luk6xff/GarageDoorKeypad/keypad/Src/StateMachine/state_processing.h

/*
 * state_processing.h
 *
 *  Created on: Jul 22, 2021
 *      Author: luk6xff
 */

#ifndef STATEMACHINE_STATE_PROCESSING_H_
#define STATEMACHINE_STATE_PROCESSING_H_

#include "sm.h"

void state_processing(SmCtx *sm);


#endif /* STATEMACHINE_STATE_PROCESSING_H_ */
