luk6xff/GarageDoorKeypad/keypad/Src/StateMachine/state_programming.h

/*
 * state_programming.h
 *
 *  Created on: Jul 22, 2021
 *      Author: luk6xff
 */

#ifndef STATEMACHINE_STATE_PROGRAMMING_H_
#define STATEMACHINE_STATE_PROGRAMMING_H_

#include "sm.h"

void state_programming(SmCtx *sm);

#endif /* STATEMACHINE_STATE_PROGRAMMING_H_ */
