luk6xff/GarageDoorKeypad/keypad/Src/StateMachine/state_sleeping.h

/*
 * state_sleeping.h
 *
 *  Created on: Jul 22, 2021
 *      Author: luk6xff
 */

#ifndef STATEMACHINE_STATE_SLEEPING_H_
#define STATEMACHINE_STATE_SLEEPING_H_

#include "sm.h"

void state_sleeping(SmCtx *sm);

#endif /* STATEMACHINE_STATE_SLEEPING_H_ */
