luk6xff/GarageDoorKeypad/keypad/Src/StateMachine/states.h

/*
 * states.h
 *
 *  Created on: Jul 22, 2021
 *      Author: luk6xff
 */

#ifndef STATEMACHINE_STATES_H_
#define STATEMACHINE_STATES_H_

#include "state_processing.h"
#include "state_sleeping.h"
#include "state_programming.h"

#endif /* STATEMACHINE_STATES_H_ */
