luk6xff/GarageDoorKeypad/common/Storage/eeprom.c

/*
 * eeprom.c
 *
 *  Created on: Jul 22, 2021
 *      Author: luk6xff
 */

#ifndef EEPROM_C_
#define EEPROM_C_

#include "eeprom.h"
#include "AT24CXX/platform/stm32cube/at24cxx-cube.h"
#include "main.h"
#include <stdio.h>

//------------------------------------------------------------------------------
// DEFINES, EXTERNS
//------------------------------------------------------------------------------
#define AT24C64_I2C_ADDR_PINS 0x00   /* |1|0|1|0|A2|A1|A0|R/W| - A2=0, A1=0, A0=0 */
extern I2C_HandleTypeDef hi2c2;

//------------------------------------------------------------------------------
// STATIC LOCAL Functions
//------------------------------------------------------------------------------
/**
 * @brief Computes a simple checksum, used for eeprom_data validation
 */
static uint32_t compute_checksum(const uint8_t *data, const uint8_t data_len);


//------------------------------------------------------------------------------
// STATIC LOCAL OBJECTS
//------------------------------------------------------------------------------

//------------------------------------------------------------------------------
static const eeprom_data eeprom_data_default =
{
	.magic = 0x12345678,
	.version = 0x00000001,
	.dev_id = 0x66BCDE77,
	.radio_configs[0] = {0xFF},
	.radio_configs[1] = {0xFF},
	.radio_configs[2] = {0xFF},
	.radio_configs[3] = {0xFF},
	.radio_configs[4] = {0xFF},
	.radio_configs[5] = {0xFF},
	.radio_configs[6] = {0xFF},
	.radio_configs[7] = {0xFF},
	.radio_configs[8] = {0xFF},
	.radio_configs[9] = {0xFF},
	.crc = 0x000000000
};

//------------------------------------------------------------------------------
static eeprom_data eeprom_data_current;

//------------------------------------------------------------------------------
// AT24C64 EEPROM
static at24cxx_cube at24c64_cube =
{
	.i2c = &hi2c2,
	.gpio_wp_port = AT24Cx_WP_GPIO_Port,
	.gpio_wp_pin = AT24Cx_WP_Pin,
};

static at24cxx at24c64 =
{
	.type = AT24C64,
};



//------------------------------------------------------------------------------
// FUNCTION DEFINITIONS
//------------------------------------------------------------------------------

//------------------------------------------------------------------------------
const eeprom_data * const eeprom_data_get_defaults()
{
	return &eeprom_data_default;
}

//------------------------------------------------------------------------------
eeprom_data * const eeprom_data_get_current()
{
	return &eeprom_data_current;
}

//------------------------------------------------------------------------------
void eeprom_init()
{
	// AT24C64 EEPROM init
	at24cxx_cube_init(&at24c64, &at24c64_cube, AT24C64_I2C_ADDR_PINS);

    if (eeprom_data_read())
    {
        // Print content
    	eeprom_data_print_current();

        // Check if settings are valid
        if (eeprom_data_get_current()->magic == eeprom_data_get_defaults()->magic && \
        	eeprom_data_get_current()->version == eeprom_data_get_defaults()->version)
        {
            printf("eeprom_data: Read eeprom settings looks ok\r\n");
            // Check if values are ok
        }
        else
        {
            printf("eeprom_data: Read eeprom settings are invalid, updating with defaults\r\n");
            if (!eeprom_data_store(eeprom_data_get_defaults()))
            {
                printf("eeprom_data: Updating eeprom with defaults failed!, setting current as defaults\r\n");
                eeprom_data_current = eeprom_data_default;
            }
            else
            {
                printf("eeprom_data: Updating eeprom with defaults succeed!\r\n");
            }
        }
    }
    else
    {
        printf("eeprom_data: Read eeprom settings failed!, setting current as defaults\r\n");
        eeprom_data_current = eeprom_data_default;
    }
}

//------------------------------------------------------------------------------
bool eeprom_data_store(const eeprom_data *data)
{
	if (at24cxx_write(&at24c64, 0, (const uint8_t*)data, sizeof(eeprom_data)) == AT24CXX_NOERR)
	{
		return true;
	}
	return false;
}

//------------------------------------------------------------------------------
bool eeprom_data_read()
{
	if (at24cxx_read(&at24c64, 0, (uint8_t*)&eeprom_data_current, sizeof(eeprom_data)) == AT24CXX_NOERR)
	{
		return true;
	}
	return false;
}

//------------------------------------------------------------------------------
void eeprom_data_print_current()
{
	printf("\r\n<<<CURRENT EEPROM DATA>>>\r\n");
	printf(".magic:0x%lx\r\n", eeprom_data_get_current()->magic);
	printf(".version:0x%lx\r\n", eeprom_data_get_current()->version);
	printf(".dev_id:0x%lx\r\n", eeprom_data_get_current()->dev_id);
	printf(".radio_config[0]: id=0x%lx, radio_code=[0x%x,0x%x,0x%x,0x%x]\r\n",
			 eeprom_data_get_current()->radio_configs[0].id,
			 eeprom_data_get_current()->radio_configs[0].code[0],
			 eeprom_data_get_current()->radio_configs[0].code[1],
			 eeprom_data_get_current()->radio_configs[0].code[2],
			 eeprom_data_get_current()->radio_configs[0].code[3]);
	printf(".radio_config[1]: id=0x%lx, radio_code=[0x%x,0x%x,0x%x,0x%x]\r\n",
			 eeprom_data_get_current()->radio_configs[1].id,
			 eeprom_data_get_current()->radio_configs[1].code[0],
			 eeprom_data_get_current()->radio_configs[1].code[1],
			 eeprom_data_get_current()->radio_configs[1].code[2],
			 eeprom_data_get_current()->radio_configs[1].code[3]);
	printf(".radio_config[2]: id=0x%lx, radio_code=[0x%x,0x%x,0x%x,0x%x]\r\n",
			 eeprom_data_get_current()->radio_configs[2].id,
			 eeprom_data_get_current()->radio_configs[2].code[0],
			 eeprom_data_get_current()->radio_configs[2].code[1],
			 eeprom_data_get_current()->radio_configs[2].code[2],
			 eeprom_data_get_current()->radio_configs[2].code[3]);
	printf(".radio_config[3]: id=0x%lx, radio_code=[0x%x,0x%x,0x%x,0x%x]\r\n",
			 eeprom_data_get_current()->radio_configs[3].id,
			 eeprom_data_get_current()->radio_configs[3].code[0],
			 eeprom_data_get_current()->radio_configs[3].code[1],
			 eeprom_data_get_current()->radio_configs[3].code[2],
			 eeprom_data_get_current()->radio_configs[3].code[3]);
	printf(".radio_config[4]: id=0x%lx, radio_code=[0x%x,0x%x,0x%x,0x%x]\r\n",
			 eeprom_data_get_current()->radio_configs[4].id,
			 eeprom_data_get_current()->radio_configs[4].code[0],
			 eeprom_data_get_current()->radio_configs[4].code[1],
			 eeprom_data_get_current()->radio_configs[4].code[2],
			 eeprom_data_get_current()->radio_configs[4].code[3]);
	printf(".radio_config[5]: id=0x%lx, radio_code=[0x%x,0x%x,0x%x,0x%x]\r\n",
			 eeprom_data_get_current()->radio_configs[5].id,
			 eeprom_data_get_current()->radio_configs[5].code[0],
			 eeprom_data_get_current()->radio_configs[5].code[1],
			 eeprom_data_get_current()->radio_configs[5].code[2],
			 eeprom_data_get_current()->radio_configs[5].code[3]);
	printf(".radio_config[6]: id=0x%lx, radio_code=[0x%x,0x%x,0x%x,0x%x]\r\n",
			 eeprom_data_get_current()->radio_configs[6].id,
			 eeprom_data_get_current()->radio_configs[6].code[0],
			 eeprom_data_get_current()->radio_configs[6].code[1],
			 eeprom_data_get_current()->radio_configs[6].code[2],
			 eeprom_data_get_current()->radio_configs[6].code[3]);
	printf(".radio_config[7]: id=0x%lx, radio_code=[0x%x,0x%x,0x%x,0x%x]\r\n",
			 eeprom_data_get_current()->radio_configs[7].id,
			 eeprom_data_get_current()->radio_configs[7].code[0],
			 eeprom_data_get_current()->radio_configs[7].code[1],
			 eeprom_data_get_current()->radio_configs[7].code[2],
			 eeprom_data_get_current()->radio_configs[7].code[3]);
	printf(".radio_config[8]: id=0x%lx, radio_code=[0x%x,0x%x,0x%x,0x%x]\r\n",
			 eeprom_data_get_current()->radio_configs[8].id,
			 eeprom_data_get_current()->radio_configs[8].code[0],
			 eeprom_data_get_current()->radio_configs[8].code[1],
			 eeprom_data_get_current()->radio_configs[8].code[2],
			 eeprom_data_get_current()->radio_configs[8].code[3]);
	printf(".radio_config[9]: id=0x%lx, radio_code=[0x%x,0x%x,0x%x,0x%x]\r\n",
			 eeprom_data_get_current()->radio_configs[9].id,
			 eeprom_data_get_current()->radio_configs[9].code[0],
			 eeprom_data_get_current()->radio_configs[9].code[1],
			 eeprom_data_get_current()->radio_configs[9].code[2],
			 eeprom_data_get_current()->radio_configs[9].code[3]);
	printf(".crc:0x%lx\r\n", eeprom_data_get_current()->crc);
}

//------------------------------------------------------------------------------
int eeprom_check_if_radio_code_exists(const uint8_t *radio_code)
{
	int ret = -1;

	if (!radio_code)
	{
		return ret;
	}

	for (size_t i = 0; i < NUM_OF_SUPPORTED_RADIOS; ++i)
	{
		if (memcmp(eeprom_data_get_current()->radio_configs[i].code, radio_code, RADIO_CODE_SIZE) == 0)
		{
			ret = i;
			break;
		}
	}

	return ret;
}

//------------------------------------------------------------------------------
bool eeprom_check_if_radio_code_id_exists(uint8_t new_code_id)
{
	// Check if given ID is already stored
	if (eeprom_data_get_current()->radio_configs[new_code_id].id == new_code_id)
	{
		printf("eeprom - A radio_code id:%d already exists.\r\n", new_code_id);
		return true;
	}
	return false;
}

//------------------------------------------------------------------------------
bool eeprom_store_new_radio_code(const uint8_t *new_code,
								const uint8_t new_code_len,
								uint8_t new_code_id)
{
	bool ret = false;

	printf("programming - eeprom_store_new_radio_code\r\n");

	if (!new_code || new_code_len != RADIO_CODE_SIZE)
	{
		printf("eeprom - New radio code not stored: invalid new code len:%d\r\n", new_code_len);
		return ret;
	}

	if (new_code_id > (NUM_OF_SUPPORTED_RADIOS-1))
	{
		printf("eeprom - New radio code not stored: invalid new_code_id:%d\r\n", new_code_id);
		return ret;
	}

	// Store a new code under a given ID
	eeprom_data_get_current()->radio_configs[new_code_id].id = new_code_id;
	memcpy(eeprom_data_get_current()->radio_configs[new_code_id].code, new_code, new_code_len);
	printf("eeprom - A new radio code: [0]=0x%x,[1]=0x%x,[2]=0x%x,[3]=0x%x stored succesfully! with ID:%d\r\n",
			new_code[0], new_code[1], new_code[2], new_code[3],new_code_id);
	// Store to eeprom
	eeprom_data_store(eeprom_data_get_current());
	ret = true;

	return ret;
}



//------------------------------------------------------------------------------
// STATIC LOCAL FUNCTIONS DEFINITIONS
//------------------------------------------------------------------------------

//------------------------------------------------------------------------------
static uint32_t compute_checksum(const uint8_t *data, const uint8_t data_len)
{
    uint8_t i;
    uint32_t sum = 0;

    for (i = 0; i < data_len; i++)
    {
    	sum = sum ^ data[i];
    }
    return sum;
}

#endif /* EEPROM_C_ */
